machdyne/blaustahl/firmware/blaustahl/blaustahl.h

/**
 * Copyright (c) 2020 Raspberry Pi (Trading) Ltd.
 *
 * SPDX-License-Identifier: BSD-3-Clause
 */

#ifndef BLAUSTAHL_H_
#define BLAUSTAHL_H_

#include <stdint.h>

#define BLAUSTAHL_VERSION "0.1.1"

#define FRAM_SIZE 8192		// 8KB
//#define FRAM_SIZE 262144	// 256KB

#define FRAM_METADATA 512	// reserved for encryption
#define FRAM_AVAILABLE (FRAM_SIZE - FRAM_METADATA)

#if FRAM_SIZE >= 262144
 #define FRAM_BIG
#endif

#include <stdbool.h>

int cdc_getchar(void);
// Drops the character if the CDC transmit FIFO is full -- right for
// echoing a keystroke. Anything written in bulk (a screen, a line, a
// transfer) must use cdc_putchar_reliable(), which waits (bounded,
// 1 s) for space: a host that polls less often than a PC's -- or is
// just busy -- otherwise loses whatever overflows the 64-byte FIFO.
void cdc_putchar(const char ch);
bool cdc_putchar_reliable(const char ch);

void blaustahl_led(uint16_t intensity);
void blaustahl_dfu(void);

// USB VENDOR CLASS COMMANDS

#define BS_CMD_NOP			0x00
#define BS_CMD_WRITE_BYTE	0x21	// <cmd> <addr:16> <data:8>
#define BS_CMD_READ_BYTE	0x31	// <cmd> <addr:16>

// PINS

#define BS_LED 			9

#define BS_FRAM_SPI		spi1
#define BS_FRAM_MOSI		11
#define BS_FRAM_MISO		12
#define BS_FRAM_SS		13
#define BS_FRAM_SCK		14

// LED SETTINGS

#define LED_STARTUP 100
#define LED_IDLE 0
#define LED_READ 100
#define LED_WRITE 250

#endif
