machdyne/blaustahl/firmware/blaustahl/mbedtls_config.h

/*
 * mbedtls configuration for Blaustahl.
 * Ported near-verbatim from the machdyne/blaustahl feature/encryption
 * branch, deliberately NOT pruned down to a minimal config yet.
 *
 * This file enables a lot of TLS/X.509/RSA/ECC functionality this
 * firmware never uses (only SHA-256 + ChaCha20-Poly1305 via PSA are
 * actually called, from crypt.c). A real minimal config would meaningfully
 * shrink the flash footprint. That pruning is deliberately deferred to
 * its own follow-up pass rather than bundled into this change --
 * mbedtls's internal dependency graph between config flags is easy to
 * get subtly wrong, and this project has already spent a long
 * debugging cycle on a much simpler hardware mismatch with no way to
 * test locally. Better to get encryption working against a config
 * that's already known to work, then prune with a known-good baseline
 * to diff against.
 */

/* Workaround for some mbedtls source files using INT_MAX without including limits.h */
#include <limits.h>

#define MBEDTLS_NO_PLATFORM_ENTROPY
#define MBEDTLS_ENTROPY_HARDWARE_ALT

#define MBEDTLS_SSL_OUT_CONTENT_LEN    2048

#define MBEDTLS_ALLOW_PRIVATE_ACCESS
#define MBEDTLS_HAVE_TIME

#define MBEDTLS_PSA_CRYPTO_C
//#define MBEDTLS_PSA_BUILTIN_HASH
//#define MBEDTLS_PSA_BUILTIN_ALG_SHA_256

//#define MBEDTLS_PSA_BUILTIN_KEY_TYPE_CHACHA20
//#define MBEDTLS_PSA_BUILTIN_ALG_CHACHA20_POLY1305
#define MBEDTLS_CHACHA20_C
#define MBEDTLS_CHACHAPOLY_C
#define MBEDTLS_POLY1305_C

#define MBEDTLS_CIPHER_MODE_CBC
#define MBEDTLS_ECP_DP_SECP192R1_ENABLED
#define MBEDTLS_ECP_DP_SECP224R1_ENABLED
#define MBEDTLS_ECP_DP_SECP256R1_ENABLED
#define MBEDTLS_ECP_DP_SECP384R1_ENABLED
#define MBEDTLS_ECP_DP_SECP521R1_ENABLED
#define MBEDTLS_ECP_DP_SECP192K1_ENABLED
#define MBEDTLS_ECP_DP_SECP224K1_ENABLED
#define MBEDTLS_ECP_DP_SECP256K1_ENABLED
#define MBEDTLS_ECP_DP_BP256R1_ENABLED
#define MBEDTLS_ECP_DP_BP384R1_ENABLED
#define MBEDTLS_ECP_DP_BP512R1_ENABLED
#define MBEDTLS_ECP_DP_CURVE25519_ENABLED
#define MBEDTLS_KEY_EXCHANGE_RSA_ENABLED
#define MBEDTLS_PKCS1_V15
#define MBEDTLS_SHA256_SMALLER
#define MBEDTLS_SSL_SERVER_NAME_INDICATION
#define MBEDTLS_AES_C
#define MBEDTLS_ASN1_PARSE_C
#define MBEDTLS_BIGNUM_C
#define MBEDTLS_CIPHER_C
#define MBEDTLS_CTR_DRBG_C
#define MBEDTLS_ENTROPY_C
#define MBEDTLS_ERROR_C
#define MBEDTLS_MD_C
#define MBEDTLS_MD5_C
#define MBEDTLS_OID_C
#define MBEDTLS_PKCS5_C
#define MBEDTLS_PK_C
#define MBEDTLS_PK_PARSE_C
#define MBEDTLS_PLATFORM_C
#define MBEDTLS_RSA_C
#define MBEDTLS_SHA1_C
#define MBEDTLS_SHA224_C
#define MBEDTLS_SHA256_C
#define MBEDTLS_SHA512_C
#define MBEDTLS_SSL_CLI_C
#define MBEDTLS_SSL_SRV_C
#define MBEDTLS_SSL_TLS_C
#define MBEDTLS_X509_CRT_PARSE_C
#define MBEDTLS_X509_USE_C
#define MBEDTLS_AES_FEWER_TABLES

/* TLS 1.2 */
#define MBEDTLS_SSL_PROTO_TLS1_2
#define MBEDTLS_KEY_EXCHANGE_ECDHE_ECDSA_ENABLED
#define MBEDTLS_GCM_C
#define MBEDTLS_ECDH_C
#define MBEDTLS_ECP_C
#define MBEDTLS_ECDSA_C
#define MBEDTLS_ASN1_WRITE_C
